kem406/hbot/20200425_195942.jpg

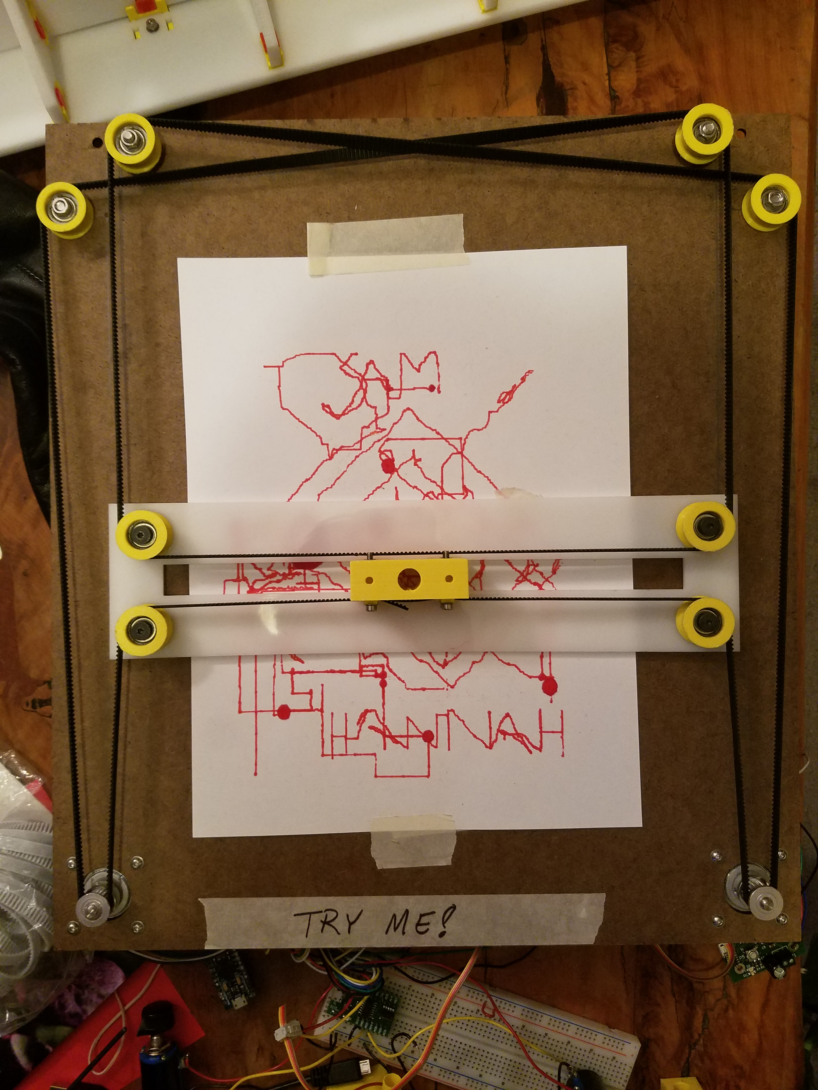
20200425_195942.jpg
